SeppeVdB/LEDM1024/LED-matrix/images.h

// This file contains the start screens of the three apps as well as some other used images.

// start screen of John Conway's Game of Life
const uint16_t game_of_life_ss[64] = {0b0000000000000000, 0b0000000000000000, 0b0001000000000000, 0b0100000000001000, 0b0010000000000000, 0b0100000000000100, 0b0100000001110010, 0b0110001000000010, 0b0010000000010101, 0b0101010100000100, 0b0001000000010101, 0b0101010100001000, 0b0000000001100010, 0b0101010100000000, 0b0000000000000000, 0b0000000000000000, 0b0000000000000000, 0b0000000000100000, 0b0110010001001000, 0b1001001010100110, 0b1000101010101000, 0b1010101110001000, 0b1000101010101010, 0b1011100010000110, 0b0110010010100101, 0b0010101100000001, 0b0000000000000000, 0b0000000000000110, 0b0000000000000000, 0b0000000000000000, 0b0000000000000000, 0b0000000000000000, 0b0001100100010100, 0b0110000010001100, 0b0010001010101010, 0b1001000101010000, 0b0010101110101010, 0b1110000101011000, 0b0001101010101010, 0b1000000010010000, 0b0000000000000000, 0b0110000000010000, 0b0000000000000000, 0b0000000000000000, 0b0000000001000100, 0b1100110000000000, 0b0000000001000001, 0b0001001000000000, 0b0000000001000101, 0b1001110000000000, 0b0000000001110101, 0b0001000000000000, 0b0000000000000001, 0b0000110000000000, 0b0000000000000000, 0b0000000000000000, 0b0000000000000000, 0b0000000000100010, 0b0000000000000000, 0b0000000000010100, 0b0000000000000000, 0b0000000000001000, 0b0000000000000000, 0b0000000000000000};

// start screen of Snake
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
